lab11/polypoint/contiki/apps/pp_noslots_common/pp_noslots_common.h

#ifndef POLYPOINT_COMMON_H
#define POLYPOINT_COMMON_H

/***********************
 ** CONFIGURATION MACROS
 */
#define DWT_PRF_64M_RFDLY 514.462f

#define TAG 1
#define ANCHOR 2

//#define DW_DEBUG
//#define DW_CAL_TRX_DELAY

// If set, the anchor will sort the ranges as they arrive
#define SORT_MEASUREMENTS

#ifdef  SORT_MEASUREMENTS
#define TARGET_PERCENTILE 0.10
#define REPORT_PERCENTILE_ONLY
//#define REPORT_PERCENTILE_VIA_UART
#endif

#define MSG_TYPE_PP_NOSLOTS_TAG_POLL   0x80
#define MSG_TYPE_PP_NOSLOTS_ANC_FINAL  0x81

#define ANCHOR_CAL_LEN (0.914-0.18) //0.18 is post-over-air calibration

#define MAX_VALID_ANCHORS 255
#define INVALID_ANCHOR_ID 255
_Static_assert(MAX_VALID_ANCHORS == INVALID_ANCHOR_ID, "The code assumes this. The different names just make it easier to read");
#define NUM_ANCHORS 18

#define DW1000_PANID 0xD100

#define DELAY_MASK 0x00FFFFFFFE00
#define SPEED_OF_LIGHT 299702547.0
#define NUM_ANTENNAS 3
#define NUM_RANGING_CHANNELS 3
#define NUM_MEASUREMENTS (NUM_ANTENNAS*NUM_ANTENNAS*NUM_RANGING_CHANNELS)

// This controls the minimum number of measurements per anchor that must be
// received for a range event with that anchor to be considered valid. It only
// affects the REPORT_PERCENTILE_ONLY case
#define MINIMUM_MEASUREMENTS_PER_ANCHOR 10
_Static_assert(MINIMUM_MEASUREMENTS_PER_ANCHOR <= NUM_MEASUREMENTS, "Impossible number of measurements");

// Range estimates that fall outside this range are thrown away to speed up processing
#define MIN_VALID_RANGE_IN_CM -100
#define MAX_VALID_RANGE_IN_CM (50*100)

#define DW1000_ANTENNA_DELAY_RX 0
#define DW1000_ANTENNA_DELAY_TX 0

#ifdef DW_DEBUG
#if WATCHDOG_CONF_ENABLE
#error Debug will be too slow for the watchdog
#endif
#endif

/****************************************************** MEASURED TIMES */
// n.b. RTIMER_SECOND on this platform has ~33 us precision

#define CMN_GUARD_US			33

#define TAG_SQ_START_TO_POLL_SFD_HIGH_US	574  // 896 @ 8 mhz
#define ANC_MYSTERY_STARTUP_DELAY_US	110  // measured 100-140

#define CMN_SET_SUBSEQ_TIME_US		270  // measured 462 @ 8mhz, 268 @ 16 mhz
#define TAG_ANC_TIMER_MISMATCH_GUARD_US	 20  // just enough to push CMN_SET_SUBSEQ_TIME_US up one timer tick

#define ANC_RX_AND_PROCESS_TAG_POLL_US	120  // 16mhz: meas 119.8; 8mhz: 220, measured 213.8 SFD -> done

#define ANC_FINAL_RX_PKT_TIME_US	398  // 8mhz: 398; 16mhz: 256
#define ANC_FINAL_RX_PKT_MEMCPY_TIME_US	 79  // 8mhz: 120
#define ANC_FINAL_RX_PKT_PRINTF_TIME_US	150
#define ANC_FINAL_RX_PKT_GUARD_US	100
#ifdef DW_DEBUG
#define ANC_FINAL_RX_TIME_ON_TAG	(\
		ANC_FINAL_RX_PKT_TIME_US +\
		ANC_FINAL_RX_PKT_MEMCPY_TIME_US +\
		ANC_FINAL_RX_PKT_PRINTF_TIME_US +\
		ANC_FINAL_RX_PKT_GUARD_US\
		)
#else
#define ANC_FINAL_RX_TIME_ON_TAG	(\
		ANC_FINAL_RX_PKT_TIME_US +\
		ANC_FINAL_RX_PKT_MEMCPY_TIME_US +\
		ANC_FINAL_RX_PKT_GUARD_US\
		)
#endif

#define ANC_FINAL_INITIAL_DELAY_HACK_VALUE 300	// See note in anchor.c
#define ANC_FINAL_TIME_TO_FIRST_RX_HACK_VALUE 1125 // same note


#ifdef DW_DEBUG
// lots of headroom for printfs
#define POLL_TO_SS_US		 5000
#define SS_TO_SQ_US		 3000
#define ALL_ANC_FINAL_US	80000
#define INTERVAL_DELAY_US	  2e6
#else
#define POLL_TO_SS_US		(TAG_SQ_START_TO_POLL_SFD_HIGH_US+ANC_RX_AND_PROCESS_TAG_POLL_US+CMN_GUARD_US)
#define SS_TO_SQ_US		(CMN_SET_SUBSEQ_TIME_US+TAG_ANC_TIMER_MISMATCH_GUARD_US)
#define ALL_ANC_FINAL_US	(ANC_FINAL_TIME_TO_FIRST_RX_HACK_VALUE + (NUM_ANCHORS*ANC_FINAL_RX_TIME_ON_TAG))
//#define INTERVAL_DELAY_US	100e3
#endif

#define US_TO_RT(_us) (RTIMER_SECOND * ((_us)/1e6))

#define APP_US_TO_DEVICETIMEU32(_microsecu)\
	(\
	 (uint32_t) ( ((_microsecu) / (double) DWT_TIME_UNITS) / 1e6 )\
	)
// uint32_t delay_time = temp + (APP_US_TO_DEVICETIMEU32(TAG_SEND_POLL_DELAY_US) >> 8);
#define SPI_US_PER_BYTE		0.94	// 0.94 @ 8mhz, 0.47 @ 16mhz
#define SPI_US_BETWEEN_BYTES	0.25	// 0.25 @ 8mhz, 0.30 @ 16mhz
#define SPI_SLACK_US		200	// 200 @ 8mhz, 150 @ 16mhz
#define DW_DELAY_FROM_PKT_LEN(_len)\
	(\
	 APP_US_TO_DEVICETIMEU32(\
		 SPI_US_PER_BYTE * (_len) + SPI_US_BETWEEN_BYTES * (_len) + SPI_SLACK_US\
		 ) >> 8\
	)
#define DW_DELAY_FROM_US(_us)\
	(\
	 APP_US_TO_DEVICETIMEU32((_us)) >> 8\
	)


#define REVISED_SPI_US_PER_BYTE		0.62  // time per byte during pkt cpoy
#define REVISED_DELAY_PKT_OVERHEAD	(33.2 + 31.25) // time read_timestamp -> copy + fin copy -> done
#define REVISED_PREAMBLE_US		160
#define REVISED_DELAY_FROM_PKT_LEN_US(_len)\
	(\
	 REVISED_SPI_US_PER_BYTE * (_len) + REVISED_DELAY_PKT_OVERHEAD + REVISED_PREAMBLE_US\
	)


extern const double txDelayCal[(1+NUM_ANCHORS)*3];

struct ieee154_header {
	uint8_t frameCtrl[2];                             //  frame control bytes 00-01
	uint8_t seqNum;                                   //  sequence_number 02
	uint8_t panID[2];                                 //  PAN ID 03-04
	uint8_t destAddr[8];
	uint8_t sourceAddr[8];
};

struct ieee154_footer {
	uint8_t fcs[2] ;                                  //  we allow space for the CRC as it is logically part of the message. However ScenSor TX calculates and adds these bytes.
};

struct pp_tag_poll  {
	struct ieee154_header header;
	uint8_t message_type;
	uint8_t roundNum;
	uint8_t subsequence;
	uint8_t reply_after_subsequence;
	uint16_t anchor_reply_window_in_us;
	uint16_t anchor_reply_slot_time_in_us;
	struct ieee154_footer footer;
} __attribute__ ((__packed__));

struct pp_anc_final {
	struct ieee154_header header;
	uint8_t message_type;
	uint8_t anchor_id;
	uint8_t final_antenna;
	uint32_t dw_time_sent;
	uint64_t TOAs[NUM_MEASUREMENTS+1];
	struct ieee154_footer footer;
} __attribute__ ((__packed__));


_Static_assert(offsetof(struct pp_tag_poll, message_type) == offsetof(struct pp_anc_final, message_type),\
			"message_type field at inconsistent offsets");


uint8_t subsequence_number_to_channel (uint8_t subseq_num);
uint8_t subsequence_number_to_antenna (uint8_t role, uint8_t subseq_num);
void set_ranging_broadcast_subsequence_settings (uint8_t role,
                                                 uint8_t subseq_num,
                                                 bool reset);
int app_dw1000_init (
		int HACK_role,
		int HACK_EUI,
		void (*txcallback)(const dwt_callback_data_t *),
		void (*rxcallback)(const dwt_callback_data_t *)
		);



#ifdef DW_DEBUG
#define DEBUG_P(...)\
	printf("[%u %u]  ", global_round_num, global_subseq_num); printf(__VA_ARGS__)
#else
#define DEBUG_P(...)
#endif

#ifdef DW_DEBUG
#define PDBL(dbl)\
{\
	int64_t _dbl1000 = (int64_t)(dbl*1000);\
	printf(# dbl ": %lld.%lld\r\n", _dbl1000/1000, _dbl1000%1000);\
}
#else
#define PDBL(dbl)
#endif

#define MIN(_a, _b) ((_a < _b) ? (_a) : (_b))
#define MAX(_a, _b) ((_a > _b) ? (_a) : (_b))

#define DEBUG_B6_LOW\
	GPIO_CLR_PIN(GPIO_PORT_TO_BASE(GPIO_B_NUM), GPIO_PIN_MASK(6))
#define DEBUG_B6_HIGH\
	GPIO_SET_PIN(GPIO_PORT_TO_BASE(GPIO_B_NUM), GPIO_PIN_MASK(6))
#define DEBUG_B6_INIT\
	GPIO_SET_OUTPUT(GPIO_PORT_TO_BASE(GPIO_B_NUM), GPIO_PIN_MASK(6))

#define DEBUG_B5_LOW\
	GPIO_CLR_PIN(GPIO_PORT_TO_BASE(GPIO_B_NUM), GPIO_PIN_MASK(5))
#define DEBUG_B5_HIGH\
	GPIO_SET_PIN(GPIO_PORT_TO_BASE(GPIO_B_NUM), GPIO_PIN_MASK(5))
#define DEBUG_B5_INIT\
	GPIO_SET_OUTPUT(GPIO_PORT_TO_BASE(GPIO_B_NUM), GPIO_PIN_MASK(5))

#define DEBUG_B4_LOW\
	GPIO_CLR_PIN(GPIO_PORT_TO_BASE(GPIO_B_NUM), GPIO_PIN_MASK(4))
#define DEBUG_B4_HIGH\
	GPIO_SET_PIN(GPIO_PORT_TO_BASE(GPIO_B_NUM), GPIO_PIN_MASK(4))
#define DEBUG_B4_INIT\
	GPIO_SET_OUTPUT(GPIO_PORT_TO_BASE(GPIO_B_NUM), GPIO_PIN_MASK(4))

#endif // POLYPOINT_COMMON_H
