lab11/polypoint/contiki/apps/pp_noslots_tag/pp_noslots_tag.c

#include "contiki.h"
#include "sys/rtimer.h"
#include "dev/leds.h"
#include "deca_device_api.h"
#include "deca_regs.h"
#include "dw1000.h"
#include "dev/ssi.h"
#include "cpu/cc2538/lpm.h"
#include "dbg.h"
#include "dev/watchdog.h"

#include "net/rime/broadcast.h"
#include "net/ip/uip.h"
#include "net/ip/uip-udp-packet.h"
#include "net/ip/uiplib.h"
#include "net/ipv6/uip-ds6-route.h"
#include "net/ipv6/uip-ds6-nbr.h"

#include <stddef.h>
#include <stdint.h>
#include <string.h>
#include <stdio.h>
#include <math.h>

#include "pp_noslots_common.h"

//#define DEBUG_NET 1
#if DEBUG_NET
#include <stdio.h>
#define PRINTF(...) printf(__VA_ARGS__)
#define PRINT6ADDR(addr) PRINTF(" %02x%02x:%02x%02x:%02x%02x:%02x%02x:%02x%02x:%02x%02x:%02x%02x:%02x%02x ", ((uint8_t *)addr)[0], ((uint8_t *)addr)[1], ((uint8_t *)addr)[2], ((uint8_t *)addr)[3], ((uint8_t *)addr)[4], ((uint8_t *)addr)[5], ((uint8_t *)addr)[6], ((uint8_t *)addr)[7], ((uint8_t *)addr)[8], ((uint8_t *)addr)[9], ((uint8_t *)addr)[10], ((uint8_t *)addr)[11], ((uint8_t *)addr)[12], ((uint8_t *)addr)[13], ((uint8_t *)addr)[14], ((uint8_t *)addr)[15])
#define PRINTLLADDR(lladdr) PRINTF(" %02x:%02x:%02x:%02x:%02x:%02x ",lladdr->addr[0], lladdr->addr[1], lladdr->addr[2], lladdr->addr[3],lladdr->addr[4], lladdr->addr[5])
#else
#define PRINTF(...)
#define PRINT6ADDR(addr)
#endif

#define ADDR_ALL_ROUTERS "ff02::2"
#define MAX_IPv6_PKT     127

/*---------------------------------------------------------------------------*/
PROCESS(polypoint_tag, "Polypoint-tag");
AUTOSTART_PROCESSES(&polypoint_tag);
static char subsequence_task(struct rtimer *rt, void* ptr);
static struct rtimer subsequence_timer;
/* virtualized in app timer instead
static char substate_task(struct rtimer *rt, void* ptr);
static struct rtimer substate_timer;
*/
/*---------------------------------------------------------------------------*/

#define TAG_EUI 0

/**************
 * GLOBAL STATE
 */

static uint8_t global_round_num = 0xFF;
static uint8_t global_subseq_num = 0xFF;

static uint64_t global_poll_send_times[NUM_MEASUREMENTS+1] = {0};
static uint64_t global_anchor_TOAs[NUM_ANCHORS][NUM_MEASUREMENTS+1] = {{0}};
static uint64_t global_anchor_final_send_times[NUM_ANCHORS] = {0};
static uint64_t global_final_TOAs[NUM_ANCHORS] = {0};
static uint8_t global_anchor_final_antenna[NUM_ANCHORS] = {0};

// This approach to mapping ids to slots trades memory for time
static uint8_t global_anchor_id_to_idx[MAX_VALID_ANCHORS+1];
static uint8_t global_anchor_idx_to_id[NUM_ANCHORS];
static unsigned global_anchor_id_map_count;
_Static_assert((MAX_VALID_ANCHORS+1) <= 256, "Need to increase global_anchor_id_map array size (and probably lots of other uint8_t refs to anchor id)");

static struct pp_tag_poll pp_tag_poll_pkt;

static struct uip_udp_conn *client_conn;


static void insert_sorted(int arr[], int new, unsigned end) {
	unsigned insert_at = 0;
	while ((insert_at < end) && (new >= arr[insert_at])) {
		insert_at++;
	}
	if (insert_at == end) {
		arr[insert_at] = new;
	} else {
		while (insert_at <= end) {
			int temp = arr[insert_at];
			arr[insert_at] = new;
			new = temp;
			insert_at++;
		}
	}
}

static uint8_t anchor_id_to_idx(uint8_t anchor_id) {
	if (global_anchor_id_to_idx[anchor_id] == INVALID_ANCHOR_ID) {
		if (global_anchor_id_map_count == NUM_ANCHORS) {
			return INVALID_ANCHOR_ID;
		} else {
			global_anchor_id_to_idx[anchor_id] = global_anchor_id_map_count;
			global_anchor_idx_to_id[global_anchor_id_map_count] = anchor_id;
			return global_anchor_id_map_count++;
		}
	} else {
		return global_anchor_id_to_idx[anchor_id];
	}
}

static double dwtime_to_dist(double dwtime, unsigned anchor_id, unsigned subseq) {
	double dist = dwtime * DWT_TIME_UNITS * SPEED_OF_LIGHT;
	dist += ANCHOR_CAL_LEN;
	dist -= txDelayCal[anchor_id*NUM_RANGING_CHANNELS + subsequence_number_to_channel(subseq)];
	return dist;
}

static void compute_results() {
	DEBUG_B6_HIGH;
#ifdef REPORT_PERCENTILE_ONLY
	char pkt[MAX_IPv6_PKT] = {0};
	unsigned pkt_offset = 0;
#endif

	unsigned i;
	for(i=0; i < global_anchor_id_map_count; i++){
		unsigned j;
#ifdef REPORT_PERCENTILE_VIA_UART
		printf("\r\ntagstart id:%d anc:%d\r\n",i,global_anchor_id_to_idx[i]);
#endif
		/*
		for (j=0; j < NUM_MEASUREMENTS+1; j++) {
			printf("%02d: ts %llu aa %llu af %llu tf %llu\r\n",
					j,
					global_poll_send_times[j],
					global_anchor_TOAs[i][j],
					global_anchor_final_send_times[i],
					global_final_TOAs[i]
			      );
		}
		printf("\r\n");
		*/

		//TODO: This assumes that the anchor antenna increments each subsequence (which it does), but this will break if that's not the case
		double tRF = (double)(global_anchor_TOAs[i][NUM_MEASUREMENTS]);
		double tSP = (double)(global_poll_send_times[global_anchor_final_antenna[i]]);
		double tSF = (double)(global_poll_send_times[NUM_MEASUREMENTS]);
		double tRP = (double)(global_anchor_TOAs[i][global_anchor_final_antenna[i]]);

		// Find a multiplier for the crystal offset between tag and anchor
		double anchor_over_tag = (tRF-tRP)/(tSF-tSP);

		// 2-way ToF from last round
		double tSR = (double)(global_anchor_final_send_times[i]);
		double tRR = (double)(global_final_TOAs[i]);
		double tTOF = (tRF-tSR)-(tSF-tRR)*anchor_over_tag;
		// Want one-way TOF
		tTOF /= 2;

		/*
		double dist = dwtime_to_dist(tTOF, i+1, 0);
		int64_t dist_times_1000000 = (int64_t)(dist*1000000);
		printf("**[%02d %02d] %lld.%lld\r\n", i+1, 0, dist_times_1000000/1000000,dist_times_1000000%1000000);
		*/

		// ancTOA = tagSent + twToF + offset

#ifdef SORT_MEASUREMENTS
		int dists_times_100[NUM_MEASUREMENTS] = {0};
#endif
		for (j=0; j < NUM_MEASUREMENTS; j++) {
			//TODO: This assumes that the anchor antenna increments each subsequence (which it does), but this will break if that's not the case
			double AA = (double)(global_anchor_TOAs[i][j]-global_anchor_TOAs[i][global_anchor_final_antenna[i]]);
			double PS = (double)(global_poll_send_times[j]-global_poll_send_times[global_anchor_final_antenna[i]]);
			double ToF = AA - PS*anchor_over_tag + tTOF;
			double dist = dwtime_to_dist(ToF, i+1, j);
#ifdef SORT_MEASUREMENTS
			int dist_times_100 = (int)(dist*100);
			// Convert invalid values to a large number so that they
			// run through the sort algorithm in minimal time and
			// are easy to discard when doing the %ile measurements
			if ((dist_times_100 < MIN_VALID_RANGE_IN_CM) || (dist_times_100 > MAX_VALID_RANGE_IN_CM)) {
				dist_times_100 = MAX_VALID_RANGE_IN_CM;
			}
			insert_sorted(dists_times_100, dist_times_100, j);
#else // SORT_MEASUREMENTS
#ifdef DW_DEBUG
			int64_t dist_times_1000000 = (int64_t)(dist*1000000);
			printf("[%02d %02d] %lld.%lld\r\n", i+1, j, dist_times_1000000/1000000,dist_times_1000000%1000000);
#else
			int dist_times_100 = (int)(dist*100);
			printf("%d.%d ", dist_times_100/100, dist_times_100%100);
#endif // DW_DEBUG
#endif // !SORT_MEASUREMENTS
		}

#ifdef SORT_MEASUREMENTS
#ifdef REPORT_PERCENTILE_ONLY
		{
			DEBUG_B6_LOW;
			unsigned num_valid = 0;
			int k;
			for (k=0; k < NUM_MEASUREMENTS; k++) {
				if (dists_times_100[k] < MAX_VALID_RANGE_IN_CM) {
					num_valid++;
				} else {
					// Can safely break b/c dists_times_100 is sorted
					break;
				}
			}

			if (num_valid < MINIMUM_MEASUREMENTS_PER_ANCHOR) {
				continue;
			} else {
				unsigned bot = num_valid*TARGET_PERCENTILE;
				unsigned top = num_valid*TARGET_PERCENTILE+1;
				int perc =
					dists_times_100[bot] +
					(dists_times_100[top] - dists_times_100[bot]) * (NUM_MEASUREMENTS*TARGET_PERCENTILE - (float) bot);
#ifdef REPORT_PERCENTILE_VIA_UART
				printf("%d:%d.%02d ",
						global_anchor_idx_to_id[i],
						perc/100,
						perc%100);
#endif
				pkt_offset += sprintf(pkt+pkt_offset,
						"%d:%d.%02d ",
						global_anchor_idx_to_id[i],
						perc/100,
						perc%100);
			}
			DEBUG_B6_HIGH;
		}
#else  // REPORT_PERCENTILE_ONLY
		printf("%d: ", global_anchor_idx_to_id[i]);
		for (j=0; j < NUM_MEASUREMENTS; j++) {
			int dist_times_100 = dists_times_100[j];
			printf("%d.%d ", dist_times_100/100, dist_times_100%100);
		}
#endif // !REPORT_PERCENTILE_ONLY
#endif // SORT_MEASUREMENTS
	}
#ifdef REPORT_PERCENTILE_ONLY
#ifdef REPORT_PERCENTILE_VIA_UART
	printf("\r\n");
#endif
	pkt[pkt_offset++] = '!';
#else
	printf("\r\ndone\r\n");
#endif

	// Send measurement over radio
	PRINTF("(pkt: %s)\n", pkt);
	uip_udp_packet_send(client_conn, pkt, pkt_offset);
	DEBUG_B6_LOW;
}

static void send_pkt(bool is_final){
	const uint16_t tx_frame_length = sizeof(struct pp_tag_poll);
	pp_tag_poll_pkt.header.seqNum++;
	pp_tag_poll_pkt.message_type = MSG_TYPE_PP_NOSLOTS_TAG_POLL;
	pp_tag_poll_pkt.subsequence = global_subseq_num;

	//Make sure we're out of rx mode before attempting to transmit
	dwt_forcetrxoff();

	// Tell the DW1000 about the packet
	dwt_writetxfctrl(tx_frame_length, 0);

	uint32_t temp = dwt_readsystimestamphi32();
	uint32_t delay_time = temp + DW_DELAY_FROM_PKT_LEN(tx_frame_length);
	delay_time &= 0xFFFFFFFE; //Make sure last bit is zero
	dwt_setdelayedtrxtime(delay_time);
	global_poll_send_times[global_subseq_num] = ((uint64_t)delay_time) << 8;

	// Write the data
	dwt_writetxdata(tx_frame_length, (uint8_t*) &pp_tag_poll_pkt, 0);

	// Start the transmission
	int err;
	if (is_final) {
		dwt_setrxaftertxdelay(1); // us
		err = dwt_starttx(DWT_START_TX_DELAYED | DWT_RESPONSE_EXPECTED);
	} else {
		err = dwt_starttx(DWT_START_TX_DELAYED);
	}

	// MP bug - TX antenna delay needs reprogramming as it is not preserved
	dwt_settxantennadelay(DW1000_ANTENNA_DELAY_TX);

	if (err == DWT_SUCCESS) {
		DEBUG_P("Sent TAG_POLL  (%u)\r\n", global_subseq_num);
	} else {
		DEBUG_P("Error sending TAG_POLL: %d\r\n", err);
		DEBUG_P("Start %lu, goal %lu, now %lu\r\n",
				temp, delay_time, dwt_readsystimestamphi32());
	}
}

// Triggered after a TX
void app_dw1000_txcallback (const dwt_callback_data_t *txd) {
	//NOTE: No need for tx timestamping after-the-fact (everything's done beforehand)
}

#define RX_PKT_BUF_LEN	256
_Static_assert(RX_PKT_BUF_LEN >= sizeof(struct pp_anc_final), "RX_PKT_BUF_LEN too small");

// Triggered when we receive a packet
void app_dw1000_rxcallback (const dwt_callback_data_t *rxd) {
	DEBUG_B6_HIGH;
	if (rxd->event == DWT_SIG_RX_OKAY) {
		leds_toggle(LEDS_BLUE);
		uint8_t packet_type;
		uint64_t timestamp;
		uint8_t recv_pkt_buf[RX_PKT_BUF_LEN];

		// Get the timestamp first
		uint8_t txTimeStamp[5] = {0, 0, 0, 0, 0};
		dwt_readrxtimestamp(txTimeStamp);
		timestamp = ((uint64_t) (*((uint32_t*) txTimeStamp))) | (((uint64_t) txTimeStamp[4]) << 32);

		// Get the packet
		dwt_readrxdata(recv_pkt_buf, MIN(RX_PKT_BUF_LEN, rxd->datalength), 0);
		packet_type = recv_pkt_buf[offsetof(struct pp_anc_final, message_type)];

		if (packet_type == MSG_TYPE_PP_NOSLOTS_ANC_FINAL) {
			DEBUG_B6_LOW;
			struct pp_anc_final* anc_final;
			anc_final = (struct pp_anc_final*) recv_pkt_buf;

			uint8_t anchor_id = anc_final->anchor_id;
			DEBUG_P("ANC_FINAL from %u\r\n", anchor_id);

			uint8_t effective_id = anchor_id_to_idx(anchor_id);
			if (effective_id == INVALID_ANCHOR_ID) return;

			DEBUG_B6_HIGH;
			memcpy(
					&global_anchor_TOAs[effective_id],
					anc_final->TOAs,
					sizeof(anc_final->TOAs)
					);
			global_anchor_final_send_times[effective_id] = ((uint64_t)anc_final->dw_time_sent) << 8;
			global_anchor_final_antenna[effective_id] = anc_final->final_antenna;
			global_final_TOAs[effective_id] = timestamp;
		} else {
			DEBUG_P("*** ERR: RX Unknown packet type: 0x%X\r\n", packet_type);
		}
	} else {
        	//If an RX error has occurred, we're gonna need to setup the receiver again
        	//  (because dwt_rxreset within dwt_isr smashes everything without regard)
        	if (rxd->event == DWT_SIG_RX_PHR_ERROR ||
		    rxd->event == DWT_SIG_RX_ERROR ||
		    rxd->event == DWT_SIG_RX_SYNCLOSS ||
		    rxd->event == DWT_SIG_RX_SFDTIMEOUT ||
		    rxd->event == DWT_SIG_RX_PTOTIMEOUT) {
			set_ranging_broadcast_subsequence_settings(TAG, global_subseq_num, true);
		} else {
			DEBUG_P("*** ERR: rxd->event unknown: 0x%X\r\n", rxd->event);
		}
	}
	DEBUG_B6_LOW;
}


void app_init(void) {
	DEBUG_P("\r\n### APP INIT\r\n");
	int err = app_dw1000_init(TAG, TAG_EUI, app_dw1000_txcallback, app_dw1000_rxcallback);
	if (err == -1) {
		leds_on(LEDS_RED);
		DEBUG_P("--- Err init'ing DW. Trying again\r\n");
		clock_delay_usec(1e3); // sleep for a millisecond before trying again
		return app_init();
	} else {
		leds_off(LEDS_RED);
	}

	// Setup the constants in the outgoing packet
	pp_tag_poll_pkt.header.frameCtrl[0] = 0x41; // data frame, ack req, panid comp
	pp_tag_poll_pkt.header.frameCtrl[1] = 0xC8; // ext addr
	pp_tag_poll_pkt.header.seqNum = 0;
	pp_tag_poll_pkt.header.panID[0] = DW1000_PANID & 0xff;
	pp_tag_poll_pkt.header.panID[1] = DW1000_PANID >> 8;
	pp_tag_poll_pkt.header.destAddr[0] = 0xff;
	pp_tag_poll_pkt.header.destAddr[1] = 0xff;
	dw1000_populate_eui(pp_tag_poll_pkt.header.sourceAddr, TAG_EUI);

	pp_tag_poll_pkt.message_type = MSG_TYPE_PP_NOSLOTS_TAG_POLL;

	pp_tag_poll_pkt.roundNum = 0;
	pp_tag_poll_pkt.subsequence = 0;

	pp_tag_poll_pkt.reply_after_subsequence = NUM_MEASUREMENTS+NUM_RANGING_CHANNELS-1;
	pp_tag_poll_pkt.anchor_reply_window_in_us = ALL_ANC_FINAL_US;
	pp_tag_poll_pkt.anchor_reply_slot_time_in_us = ANC_FINAL_RX_TIME_ON_TAG;
}



static char subsequence_task(struct rtimer *rt, void* ptr){
	rtimer_clock_t now = RTIMER_NOW();
	rtimer_clock_t set_to;

	DEBUG_B5_HIGH;

	if (global_subseq_num < (NUM_MEASUREMENTS+NUM_RANGING_CHANNELS)) {
		set_to = now + US_TO_RT(POLL_TO_SS_US+SS_TO_SQ_US);
	} else {
		set_to = now + US_TO_RT(ALL_ANC_FINAL_US);
	}
	if (global_subseq_num <= (NUM_MEASUREMENTS+NUM_RANGING_CHANNELS+NUM_RANGING_CHANNELS))
		rtimer_set(rt, set_to, 1, (rtimer_callback_t)subsequence_task, NULL);


	if(global_subseq_num < (NUM_MEASUREMENTS+NUM_RANGING_CHANNELS)) {
		set_ranging_broadcast_subsequence_settings(TAG, global_subseq_num, false);
		send_pkt(false);
		global_subseq_num++;
	} else if (global_subseq_num < (NUM_MEASUREMENTS+NUM_RANGING_CHANNELS+NUM_RANGING_CHANNELS)) {
		set_ranging_broadcast_subsequence_settings(TAG, global_subseq_num, false);

		send_pkt(true); // enables rx
		global_subseq_num++;

		DEBUG_P("In wait period expecting ANC_FINALs\r\n");

		// anchors should begin sending ANC_FINAL
		// messages during this slot; the rx handler
		// will fill out the results array
	} else {
		set_ranging_broadcast_subsequence_settings(TAG, 0, true);
		compute_results();

		pp_tag_poll_pkt.roundNum = ++global_round_num;

		memset(global_poll_send_times, 0, sizeof(global_poll_send_times));
		memset(global_anchor_TOAs, 0, sizeof(global_anchor_TOAs));
		memset(global_anchor_final_send_times, 0, sizeof(global_anchor_final_send_times));
		memset(global_anchor_final_antenna, 0, sizeof(global_anchor_final_antenna));
		memset(global_final_TOAs, 0, sizeof(global_final_TOAs));

		unsigned i;
		for (i=0; i<global_anchor_id_map_count; i++) {
			global_anchor_id_to_idx[global_anchor_idx_to_id[i]] = INVALID_ANCHOR_ID;
		}

		global_subseq_num = 0;

		// Tickle the watchdog
		watchdog_periodic();

		// Call the timer function so the next round kickstarts
		subsequence_task(&subsequence_timer, NULL);
	}
	DEBUG_B5_LOW;

	return 1;
}

PROCESS_THREAD(polypoint_tag, ev, data) {
	PROCESS_BEGIN();

	leds_on(LEDS_ALL);

	watchdog_init();	// Contiki default sets watchdog to 1 s
	watchdog_start();

	//Keep things from going to sleep
	lpm_set_max_pm(0);


	dw1000_init();
#ifdef DW_DEBUG
	printf("Inited the DW1000 driver (setup SPI)\r\n");
#endif

	leds_off(LEDS_ALL);

#ifdef DW_DEBUG
	printf("Setting up DW1000 as a Tag.\r\n");
#endif
	/* PROGRAM BEHAVIOR
	 * Loop through states based on global_subseq_num. State execution is
	 * split, partially in the timer callback (interrupt context) and mostly
	 * in the main loop context. Item's with '+' are in the interrupt handler
	 * and '-' are in the main loop.
	 *
	 * states 0 .. NUM_MEASUREMENTS-1:
	 *   + Start t0: POLL_TO_SS timer
	 *   - Send broadcast TAG_POLL
	 *
	 *   # Sub-state triggered by t0 expiration
	 *   + Start t1: SS_TO_SQ timer
	 *   - Choose antenna and channel
	 *
	 * state NUM_MEASUREMENTS+1:
	 *   + Start t0: ALL_ANC_FINAL timer
	 *   - Set state to 0
	 *   - Send broadcast TAG_FINAL
	 *     -- Expect ANC_FINAL's from each anchor
	 *
	 *   # Sub-state triggered by t0 expiration
	 *   + Start t1: SS_PRINTF timer
	 *   - Print result of all measurements
	 *   - Reset the world
	 *     -- sets state to 0
	 *
	 */

	static uip_ipaddr_t dest_addr;

	// Setup the destination address
	uiplib_ipaddrconv(ADDR_ALL_ROUTERS, &dest_addr);

	// Setup a udp "connection"
	client_conn = udp_new(&dest_addr, UIP_HTONS(3000), NULL);
	if (client_conn == NULL) {
		// Too many udp connections
		// not sure how to exit...stupid contiki
	}
	udp_bind(client_conn, UIP_HTONS(3001));

	PRINTF("Created a connection with the server ");
	PRINT6ADDR(&client_conn->ripaddr);
	PRINTF(" local/remote port %u/%u\n",
			UIP_HTONS(client_conn->lport), UIP_HTONS(client_conn->rport));

	app_init();
	global_round_num = 0;
	global_subseq_num = 0;
	set_ranging_broadcast_subsequence_settings(TAG, 0, true);

	// Tickle the watchdog
	watchdog_periodic();

	// Kickstart things at the beginning of the loop
	rtimer_init();
	rtimer_set(&subsequence_timer, RTIMER_NOW() + US_TO_RT(10000), 1,
			(rtimer_callback_t)subsequence_task, NULL);

	DEBUG_B4_INIT;
	DEBUG_B5_INIT;
	DEBUG_B6_INIT;
	DEBUG_B4_HIGH;
	DEBUG_B5_HIGH;
	DEBUG_B6_LOW;

	while(1) {
		PROCESS_YIELD_UNTIL(ev == PROCESS_EVENT_POLL);

	}

	PROCESS_END();
}
