lab11/polypoint/software/firmware/oneway_tag.h

#ifndef __ONEWAY_TAG_H
#define __ONEWAY_TAG_H

#include "oneway_common.h"
#include "deca_device_api.h"
#include "deca_regs.h"

typedef enum {
	TSTATE_IDLE,
	TSTATE_BROADCASTS,
	TSTATE_TRANSITION_TO_ANC_FINAL,
	TSTATE_LISTENING,
	TSTATE_CALCULATE_RANGE
} tag_state_e;

// ERRORS for reporting to the TAG host what happened with ranges from different
// anchors. If an anchor didn't respond or the packet didn't go through then
// it will not be included. If the anchor did respond, then it will be included,
// and if something went wrong with the range an invalid range from below
// will be returned.

// The ANCHOR did not receive matching packets from the first three cycle.
// This prevents us from calculating clock skew, and we have to skip this
// anchor range.
#define ONEWAY_TAG_RANGE_ERROR_NO_OFFSET 0x80000001
// The anchor did not receive enough packets from the tag, so we don't have
// enough observations (ranges) to actually calculate a range to this
// anchor.
#define ONEWAY_TAG_RANGE_ERROR_TOO_FEW_RANGES 0x80000002
// Something else went wrong that we don't have pinned down.
#define ONEWAY_TAG_RANGE_ERROR_MISC 0x8000000F


// Size buffers for reading in packets
#define ONEWAY_TAG_MAX_RX_PKT_LEN 296

typedef struct {
	// Our timer object that we use for timing packet transmissions
	stm_timer_t* tag_timer;
	
	tag_state_e state;
	
	// Which subsequence slot we are on when transmitting broadcast packets
	// for ranging.
	uint8_t ranging_broadcast_ss_num;
	
	// Which slot we are in when receiving packets from the anchor.
	uint8_t ranging_listening_window_num;
	
	// Array of when we sent each of the broadcast ranging packets
	uint64_t ranging_broadcast_ss_send_times[NUM_RANGING_BROADCASTS];
	
	// How many anchor responses we have gotten
	uint8_t anchor_response_count;
	
	// Array of when we received ANC_FINAL packets and from whom
	anchor_responses_t anchor_responses[MAX_NUM_ANCHOR_RESPONSES];
	
	// These are the ranges we have calculated to a series of anchors.
	// They use the same index as the _anchor_responses array.
	// Invalid ranges are marked with INT32_MAX.
	int32_t ranges_millimeters[MAX_NUM_ANCHOR_RESPONSES];
	
	// Prepopulated struct of the outgoing broadcast poll packet.
	struct pp_tag_poll pp_tag_poll_pkt;
} oneway_tag_scratchspace_struct;

oneway_tag_scratchspace_struct *ot_scratch;

void oneway_tag_init (void *app_scratchspace);
dw1000_err_e oneway_tag_start_ranging_event ();
void oneway_tag_stop ();

#endif
