lab11/polypoint/software/include/system.h

#ifndef __SYSTEM_H
#define __SYSTEM_H

#define TRUE  1
#define FALSE 0

typedef uint8_t bool;

// Convenience functions
#define MIN(_a, _b) ((_a < _b) ? (_a) : (_b))
#define MAX(_a, _b) ((_a > _b) ? (_a) : (_b))

#endif
