lab11/polypoint/contiki/apps/polypoint_fastbaud/project-conf.h

#ifndef PROJECT_CONF_H_
#define PROJECT_CONF_H_

/*
 * @author: Brad Campbell <bradjc@umich.edu>
 */

// No need for UART
// #define STARTUP_CONF_VERBOSE 0
// #define UART_CONF_ENABLE 0

#define WATCHDOG_CONF_ENABLE 0
#define LPM_CONF_ENABLE 0

#endif /* PROJECT_CONF_H_ */

/** @} */
