lab11/polypoint/contiki/tools/rough_time_for_paper.py

#!/usr/bin/env python

import logging
log = logging.getLogger(__name__)
#logging.basicConfig(level=logging.DEBUG)
logging.basicConfig()

import sys
import argparse
import os
import glob
import numpy as np
import time
import traceback

start_time = None
end_time = None
count = 0

from scipy.optimize import fmin_bfgs

NUM_ANCHORS = 18
NUM_ANTENNAS = 3
NUM_CHANNELS = 3
NUM_MEASUREMENTS = NUM_ANTENNAS*NUM_ANTENNAS*NUM_CHANNELS
#ANCHOR_POSITIONS = np.matrix([
#    [0.055, 0.582, 1.808],
#    [4.255, 0.567, 1.756],
#    [0.826, 7.179, 1.457],
#    [4.263, 6.190, 1.620],
#    [0.0, 0.0, 0.0],
#    [0.0, 0.0, 0.0],
#    [0.0, 0.0, 0.0],
#    [0.0, 0.0, 0.0],
#    [0.0, 0.0, 0.0],
#    [0.0, 0.0, 0.0]
#]);
#ANCHOR_POSITIONS = np.matrix([
#    [11.066+1.778, 0.055, 1.666],
#    [6.403+1.778, 0.055, 1.776],
#    [0.28+1.778, 0.055, 1.908],
#    [15.713-7.582, 19.53, 1.839],
#    [0.444+0.055, 3.901, 2.180],
#    [12.603-0.055, 3.836, 2.094],
#    [0.444+0.055, 9.762, 2.224],
#    [4.148+1.778, 0.055, 1.689],
#    [0.444-0.051, 15.065, 2.145],
#    [15.713-0.055, 25.233-12.338, 1.394]
#]);





ANCHOR_POSITIONS = np.matrix([
    [15.236,    0.502,  2], # pos1
    [9.470,     0.502,  2], # pos2
    [3.856,     0.502,  2], # pos3
    [-100,      -100,   -100], #dummy
    [-100,      -100,   -100], #dummy
    [0.055,     12.955, 2], # pos6
    [3.863,     12.526, 2], # pos7
    [12.535,    -0.081, 4.646], # new pos8
    [0.055,     4.063,  2], # pos4
    [0.055,     8.228,  2], # pos5
    [-100,      -100,   -100], #dummy
    [0.916,     13.127, 4.646], # pos12
    [15.603,    3.383,  4.646], # pos13
    [6.832,     13.127, 4.646], # pos14
    [6.81,      -0.081, 4.646], # pos15
    [9.470,     0.502,  0.057], # pos16, underneath 2
    [0.898,     -0.081, 4.646], # pos17
    [3.863,     12.526, 0.057], # pos18, underneath 7
]);

if NUM_ANCHORS > len(ANCHOR_POSITIONS):
	log.warn("More anchors than known posistions")
	log.warn("If a packet is received from an anchor without a known position,")
	log.warn("this script will currently die")

# Positions not currently occupied by an anchor
#    [9.700,     12.526, 2],   # pos8
#    [19.488,    10.957, 2.5], # pos9
#    [19.488,    8.227,  2.5], # pos10

def location_optimize(x,anchor_ranges,anchor_locations):
    if(x.size == 2):
        x = np.append(x,2)
    x = np.expand_dims(x, axis=0)
    x_rep = np.tile(x, [anchor_ranges.size,1])
    r_hat = np.sqrt(np.sum(np.power((x_rep-anchor_locations),2),axis=1))
    r_hat = np.reshape(r_hat,(anchor_ranges.size,))
    ret = np.sum(np.power(r_hat-anchor_ranges,2))
    return ret

def get_line(port):
    if args.port != '-':
        # Open the serial connection
        sp = serial.Serial(
            port=args.port,
            baudrate=115200,
            bytesize=8,
            parity=serial.PARITY_NONE,
            stopbits=1,
            xonxoff=0,
            rtscts=0,
            timeout=None
        )

    while True:
        if args.port != '-':
            cur_line = sp.readline()
            cur_line = cur_line.decode("utf-8")
            cur_line = cur_line.strip()
        else:
            # Note: This won't handler EOF correctly:
            #cur_line = sys.stdin.readline().strip()
            for line in iter(sys.stdin.readline, ''):
                if 'Bringing' in line:
                    continue
                if 'SIGINT' in line:
                    continue
                if '#' in line:
                    # Ignore lines with '# Corrupted packet.'
                    continue
                if ':' in line:
                    # Handle timestamp if present
                    ts,meas = line.split(':')
                    yield (ts.strip(), meas.strip())
                else:
                    yield line.strip()
            break
        if len(cur_line) == 0:
            continue
        yield cur_line

def get_measurements(port):
    def parse_measurement(meas):
        n,f = map(float, meas.split('.'))
        m = abs(n) + abs(f)/100
        if n < 0 or f < 0:
            m = -m
        return m

    lines = get_line(port)

    # Throw away the first line as it's probably partial
    lines.next()

    while True:
        line = lines.next()
        try:
            ts, line = line
        except ValueError:
            ts = None

        if True or line[-1] == '!':
            # If the line ends in ! assume we are in the %ile only case
            meas = []
            bail = False
            for m in line.split():
                if m == '!':
                    break
                elif '.' in m:
                    try:
                        meas.append(parse_measurement(m))
                    except ValueError:
                        bail = True
                        break
                else:
                    meas.append(0.0)
            if bail:
                continue
            yield ts, meas
        elif line[0] == '[':
            raise NotImplementedError("Don't currently parse DW_DEBUG output")
        else:
            # In print all measurements case, may or may not be sorted

            # First, hunt for a 'tagstart 1' to get to the start of a round
            while line[0:8] != 'tagstart 1':
                line = lines.next()
            i = 1
            ranges = {}
            while True:
                line = lines.next()
                if line == 'done':
                    log.warn("WARN: Premature 'done' message, skipping measurement")
                    break

                ranges[i] = map(parse_measurement, line.split())
                if len(ranges) != NUM_MEASUREMENTS:
                    log.warn("WARN: Measurement with too few ranges, skipping.  Had", len(ranges))
                    break

                i += 1

                line = lines.next()
                if i < 10:
                    expect = 'tagstart {}'.format(i)
                    if line != expect:
                        log.warn("WARN: expected {} got {}. Skipping measurement".\
                                        format(expect, line))
                        break
                else:
                    if line != 'done':
                        log.warn("WARN: expected {} got {}. Skipping measurement".\
                                        format('done', line))
                        break

                    meas = []
                    for j in range(1, 11):
                        temp_array = np.array([val for val in ranges[j] if (val > -50 and val > 50*100)])
                        if temp_array.size > 0:
                            meas.append(np.percentile(temp_array, 10))
                        else:
                            meas.append(0.0)

                    yield ts, meas
                    break

try:
    import serial
except ImportError:
    print('{} requires the Python serial library'.format(sys.argv[0]))
    print('Please install it with one of the following:')
    print('')
    if PY3:
        print('   Ubuntu:  sudo apt-get install python3-serial')
        print('   Mac:     sudo port install py34-serial')
    else:
        print('   Ubuntu:  sudo apt-get install python-serial')
        print('   Mac:     sudo port install py-serial')
    sys.exit(1)

if __name__ == "__main__":
    #anchor_ranges = np.array([ 2.5106,  3.128,   4.2106])
    #anchor_locations = np.matrix([[ 4.255,  0.567,  1.756],
    #    [ 0.055,  0.582,  1.808],
    #    [ 4.263,  6.19,   1.62 ]])
    #tag_position = fmin_bfgs(
    #    f=location_optimize, 
    #    x0=np.array([0, 0, 0]),
    #    args=(anchor_ranges, anchor_locations)
    #)
    #print("Tag position: {}".format(tag_position))
    #blah = location_optimize(np.array([2.58, 2.374, 1.824]),anchor_ranges,anchor_locations)
    #print(blah)

    # Try and find the port automatically
    ports = []

    # Get a list of all USB-like names in /dev
    for name in ['tty.usbserial', 'ttyUSB', 'tty.usbmodem']:
        ports.extend(glob.glob('/dev/%s*' % name))

    ports = sorted(ports)

    if ports:
        # Found something - take it
        port_name = ports[0]
    else:
        port_name = '-'

    parser = argparse.ArgumentParser()
    parser.add_argument('-p', '--port', default=port_name,
            help="Specify a port (use '-' for stdin)")
    parser.add_argument('-a', '--always-report-range', action='store_true', default=False,
            help="Always print an estimate even if there aren't enough ranges")
    args = parser.parse_args()

    if args.port == '-':
        log.info("Reading from stdin (probably want ./PolyPointReceive | ./" + sys.argv[0])
    else:
        log.info("Reading from serial port at " + args.port)

    # TODO: Make arg
    ofile = open('log.txt', 'w')

    measurements = get_measurements(args.port)

    #Wait for comment indicating restart condition
    tag_position=np.array([0, 0, 0])
    while True:
            if start_time is None:
                start_time = time.time()

            try:
                meas = measurements.next()
            except StopIteration:
                break
            try:
                ts, meas = meas
            except ValueError:
                ts = None
            ranges = np.array(meas)

            log.debug("got meas: %s", ranges)

            #Perform trilateration processing on all received data
            sorted_ranges = np.sort(ranges)
            sorted_range_idxs = np.argsort(ranges)
            ranges = np.zeros(NUM_ANCHORS)
            range_start_idx = 0
            first_valid_idx = np.where(sorted_ranges > 0)
            first_valid_idx = first_valid_idx[0]
            if(first_valid_idx.size > 0):
                first_valid_idx = first_valid_idx[0]
            else:
                first_valid_idx = NUM_ANCHORS
            last_valid_idx = NUM_ANCHORS

            #Make sure we have enough valid ranges to get a good fix on position (3)
            num_valid_anchors = sorted_ranges.size - first_valid_idx
            log.debug("Seeing {} anchors (from {}-{})".format(num_valid_anchors, first_valid_idx, last_valid_idx))
            if(num_valid_anchors == 0):
                if args.always_report_range:
                    log.warn("Zero anchors this time... (guessing last)")
                else:
                    continue
            elif(num_valid_anchors == 1):
                if args.always_report_range:
                    log.warn("ONLY ONE ANCHOR... (guessing last)")
                else:
                    continue
            elif(num_valid_anchors == 2):
                if args.always_report_range:
                    log.debug("WARNING: ONLY TWO ANCHORS...")
                    loc_anchor_positions = ANCHOR_POSITIONS[sorted_range_idxs[first_valid_idx:last_valid_idx]]
                    loc_anchor_ranges = sorted_ranges[first_valid_idx:last_valid_idx]
                    log.debug("loc_anchor_ranges = {}".format(loc_anchor_ranges))
                    tag_position = fmin_bfgs(
                        f=location_optimize, 
                        x0=tag_position[0:2],
                        args=(loc_anchor_ranges, loc_anchor_positions)
                    )
                    tag_position = np.append(tag_position,2)
                else:
                    continue
            else:
                log.debug("SUCCESS: Enough valid ranges to perform localization...")
                loc_anchor_positions = ANCHOR_POSITIONS[sorted_range_idxs[first_valid_idx:last_valid_idx]]
                loc_anchor_ranges = sorted_ranges[first_valid_idx:last_valid_idx]
                log.debug(loc_anchor_positions)
                log.debug("loc_anchor_ranges = {}".format(loc_anchor_ranges))
                disp = True if log.isEnabledFor(logging.DEBUG) else False
                tag_position = fmin_bfgs(
                    disp=disp,
                    f=location_optimize, 
                    x0=tag_position,
                    args=(loc_anchor_ranges, loc_anchor_positions)
                )

            #if ts:
            #    print("{} {} {} {}".format(ts, tag_position[0], tag_position[1], tag_position[2]))
            #    ofile.write("{},{},{},{}\n".format(ts, tag_position[0], tag_position[1], tag_position[2]))
            #else:
            #    print("{} {} {}".format(tag_position[0], tag_position[1], tag_position[2]))
            #    ofile.write("{},{},{}\n".format(tag_position[0], tag_position[1], tag_position[2]))

            end_time = time.time()
            count += 1

print('')
print(end_time - start_time)
print((end_time - start_time) / count)
